ak66666/ThumbsUpV8_5x12KailhChocProMicro/Photos/IMG_20231113_221521098_HDR.jpg

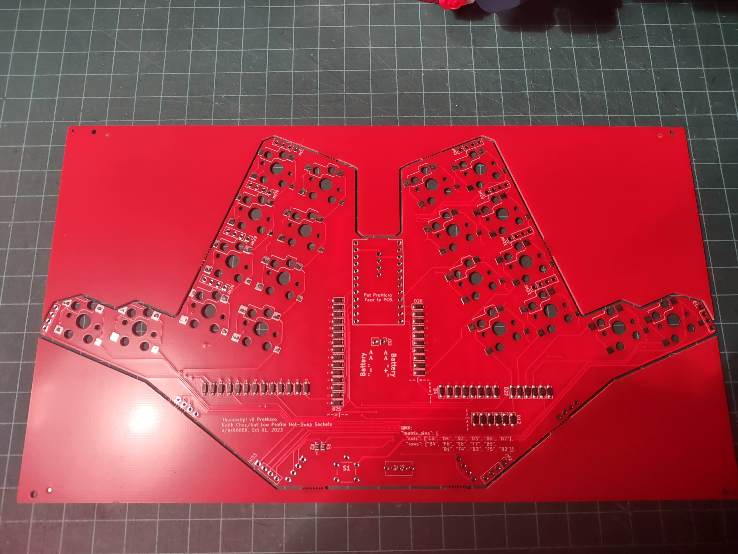
Photos/IMG_20231113_221521098_HDR.jpg
