ak66666/ThumbsUpV8_5x12KailhChocProMicro/Photos/IMG_20240220_221720754_HDR.jpg

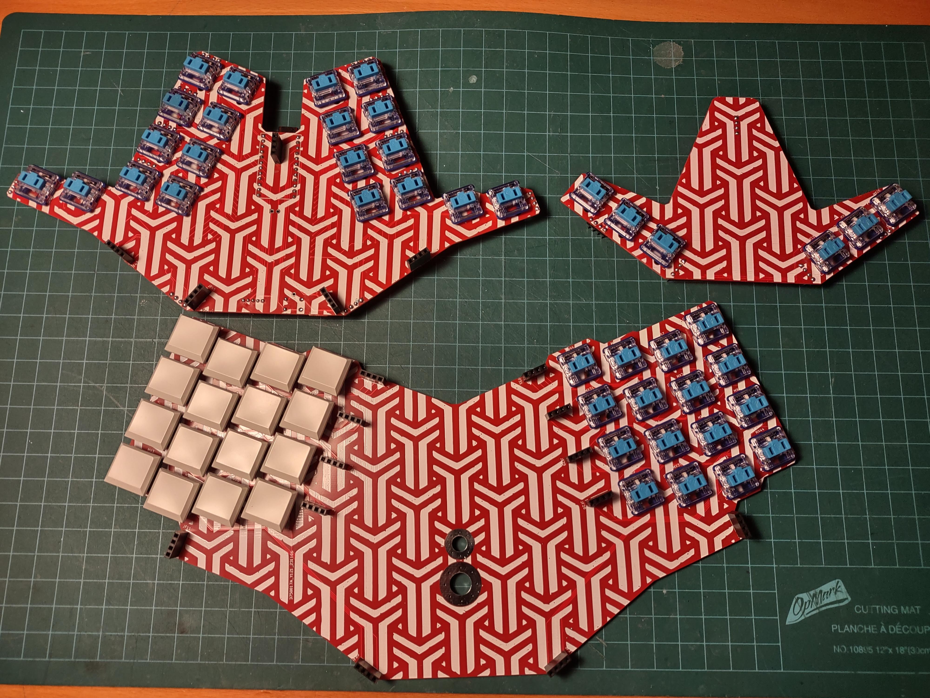
Photos/IMG_20240220_221720754_HDR.jpg
