ak66666/ThumbsUpV8_5x12KailhChocProMicro/Photos/IMG_20240220_221751057.jpg

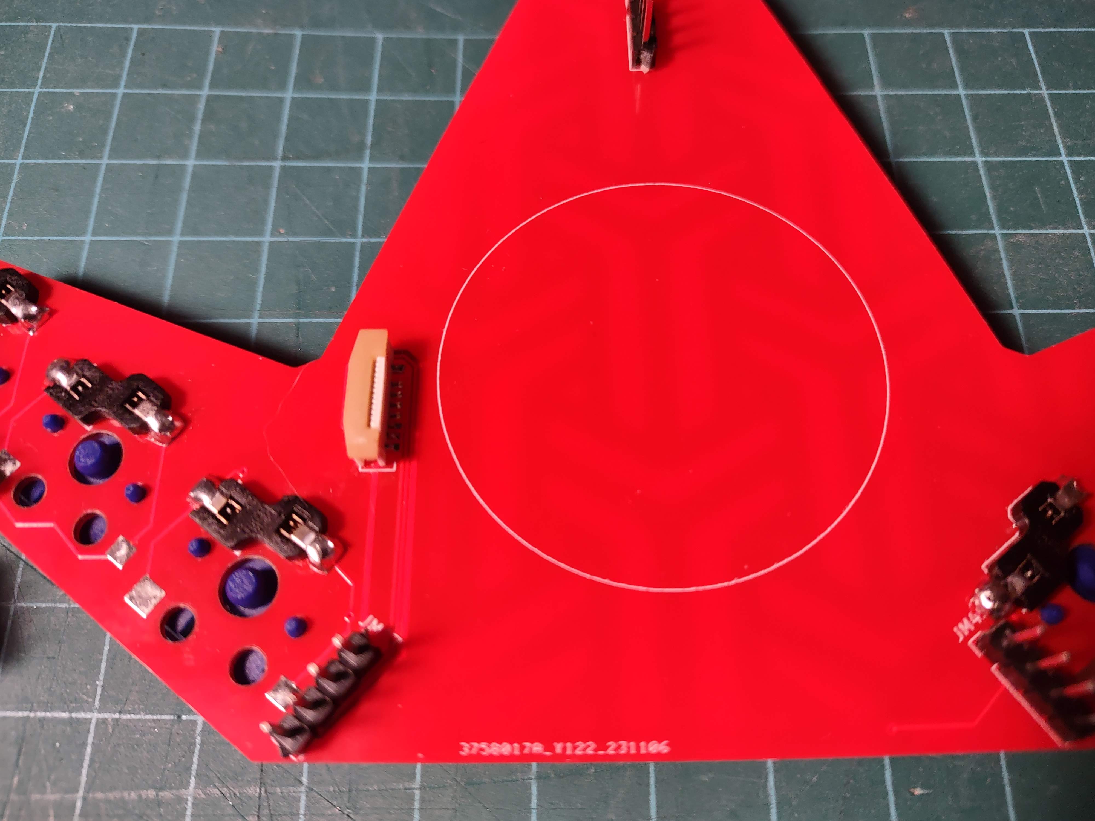
Photos/IMG_20240220_221751057.jpg
