ak66666/ThumbsUpV8_5x12KailhChocProMicro/Photos/IMG_20240220_222248993.jpg

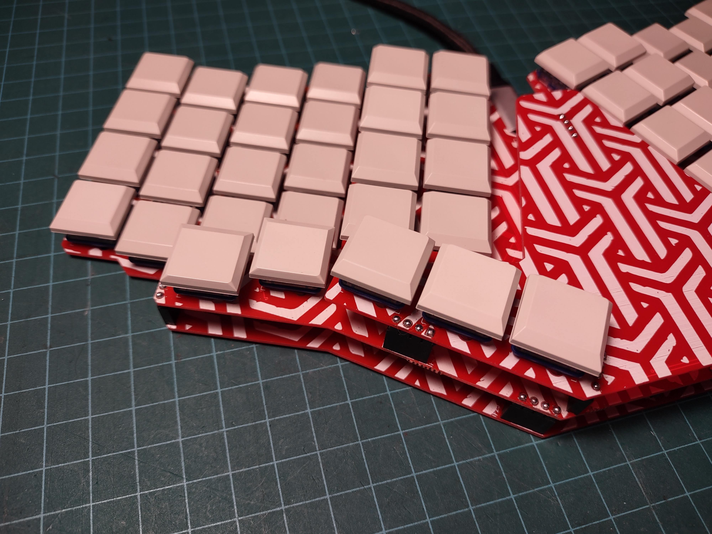
Photos/IMG_20240220_222248993.jpg
