ak66666/ThumbsUpV8_5x12KailhChocProMicro/Photos/IMG_20240220_222252121.jpg

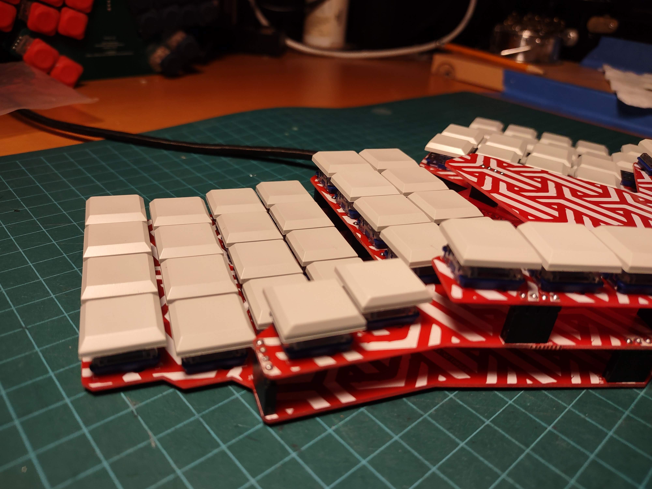
Photos/IMG_20240220_222252121.jpg
