ak66666/ThumbsUpV8_5x12KailhChocProMicro/Silkscreens/44 Key Keyboard Layout 20 pct.png

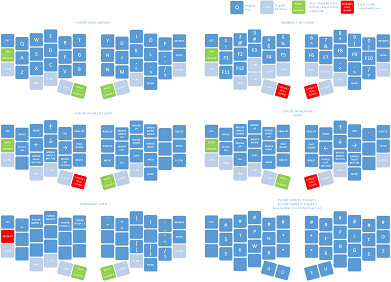
Silkscreens/44 Key Keyboard Layout 20 pct.png
