ak66666/ThumbsUpV8_5x12KailhChocProMicro/Silkscreens/Pattern.png

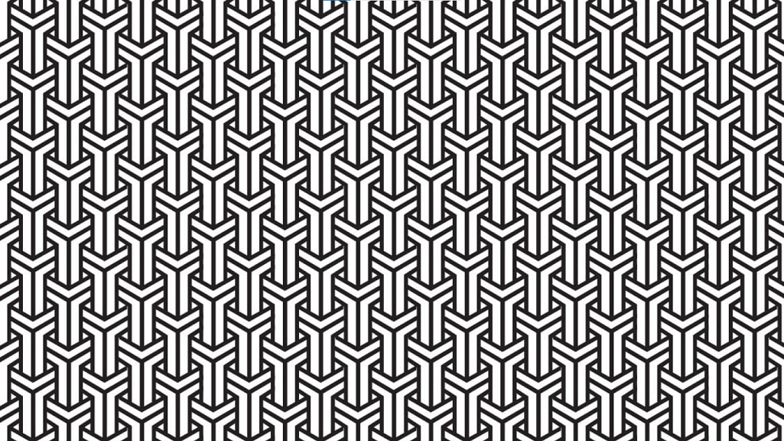
Silkscreens/Pattern.png
