ak66666/ThumbsUpV8_5x12KailhChocProMicro/Silkscreens/QWERTY.png

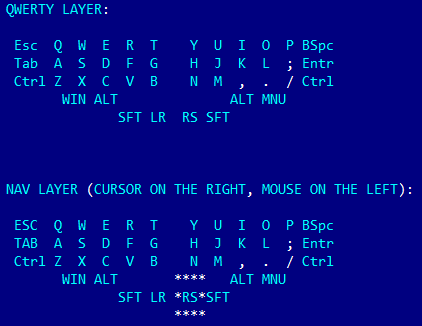
Silkscreens/QWERTY.png
